FabLab-Merida/Smars-con-Microbit/CAD/SmarsMicrobit/Chasis/Servo/SMARS_servo_wheel.stl

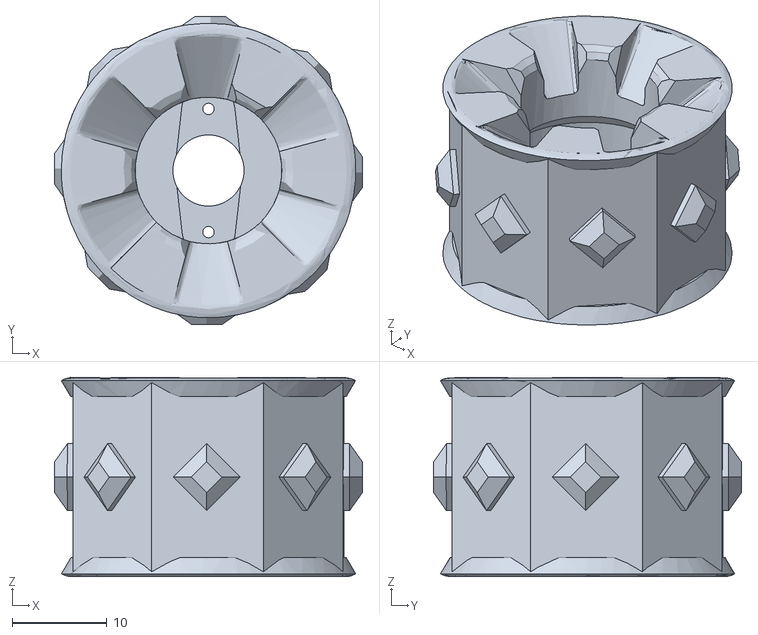
[picture p52: CAD file, 2024-05-20]
CAD/SmarsMicrobit/Chasis/Servo/SMARS_servo_wheel.stl
32.5 x 32.5 x 21.0
