FabLab-Merida/Smars-con-Microbit/CAD/SmarsMicrobit/CommonMicrobitPieces/slave_wheel_SL.stl

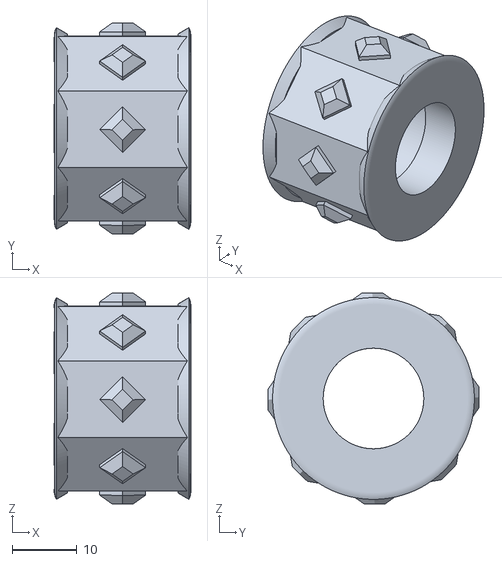
[picture p53: CAD file, 2024-05-20]
CAD/SmarsMicrobit/CommonMicrobitPieces/slave_wheel_SL.stl
21.0 x 32.5 x 32.5
