FabLab-Merida/Smars-con-Microbit/CAD/SmarsMicrobit/Sensores/Montacargas/fork_lift_a.stl

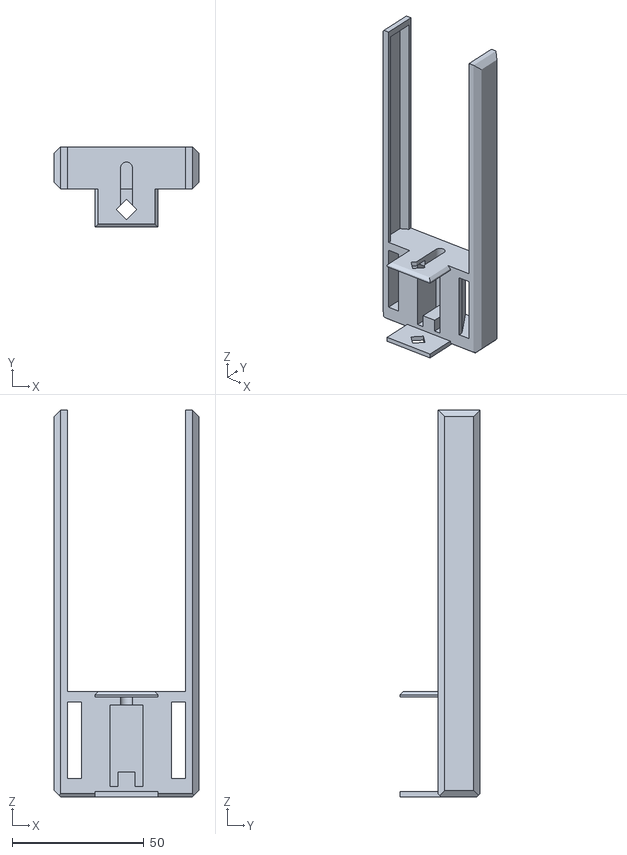
[picture p54: CAD file, 2024-05-20]
CAD/SmarsMicrobit/Sensores/Montacargas/fork_lift_a.stl
55.0 x 30.5 x 147.0
