FabLab-Merida/Smars-con-Microbit/CAD/SmarsMicrobit/Sensores/SensorCapacitivo/holder_soil_moisture.stl

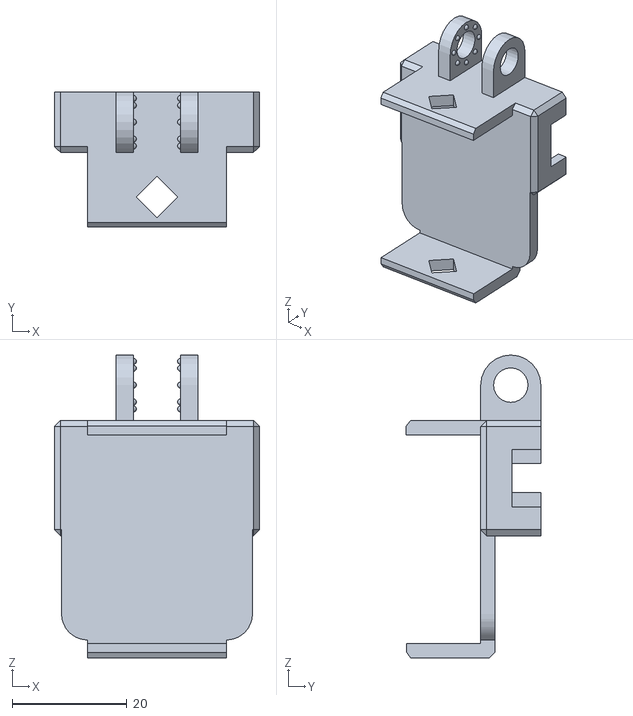
[picture p55: CAD file, 2024-05-20]
CAD/SmarsMicrobit/Sensores/SensorCapacitivo/holder_soil_moisture.stl
35.8 x 23.5 x 52.8
