FabLab-Merida/Smars-con-Microbit/CAD/SmarsMicrobit/Sensores/SensorUltrasonidos/ultrasonic_1.stl

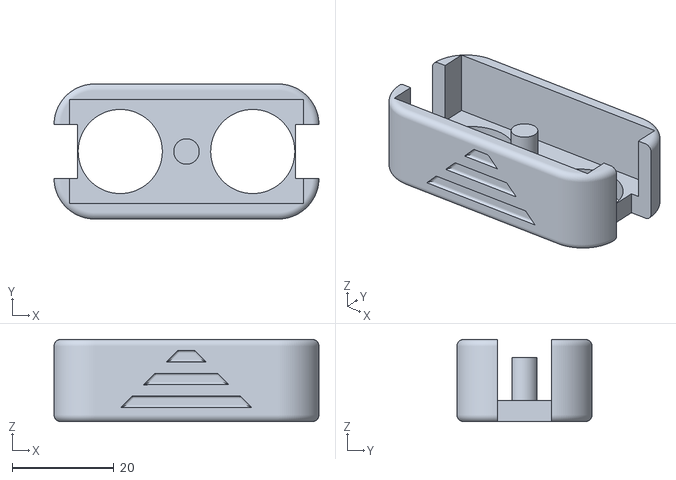
[picture p56: CAD file, 2024-05-20]
CAD/SmarsMicrobit/Sensores/SensorUltrasonidos/ultrasonic_1.stl
52.0 x 26.5 x 16.1
