FabLab-Merida/Smars-con-Microbit/CAD/SmarsMicrobit/Sensores/SmarsSensorCapacitivoV0(NoUsar)/Solid/smarsCapacitive.SLDPRT

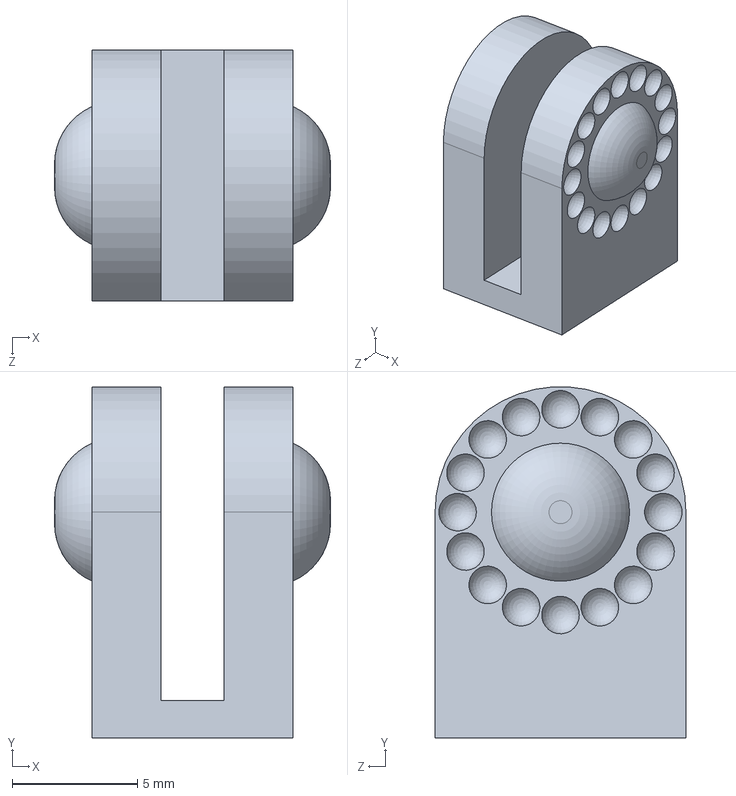
[picture p57: CAD file, 2024-05-20]
CAD/SmarsMicrobit/Sensores/SmarsSensorCapacitivoV0(NoUsar)/Solid/smarsCapacitive.SLDPRT
11.0 x 14.0 x 10.0 mm
