FabLab-Merida/Smars-con-Microbit/CAD/SmarsMicrobit/Chasis/PasoAPaso/SmarsMasterWheelStepper.stl

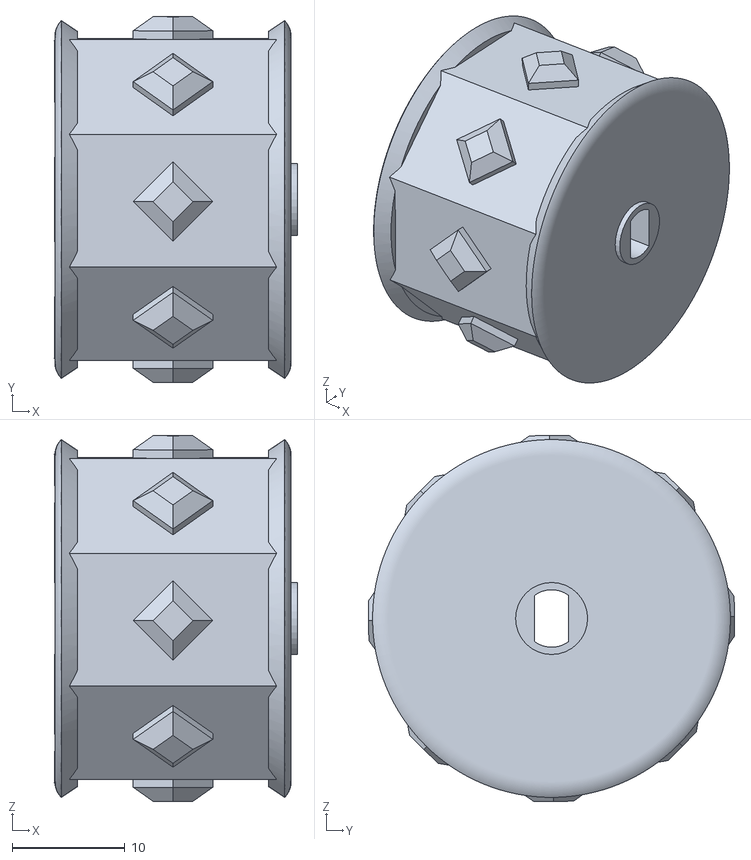
[picture p58: CAD file, 2024-05-20]
CAD/SmarsMicrobit/Chasis/PasoAPaso/SmarsMasterWheelStepper.stl
21.6 x 32.5 x 32.5
