FabLab-Merida/Smars-con-Microbit/CAD/SmarsMicrobit/CommonMicrobitPieces/mechanical_track.stl

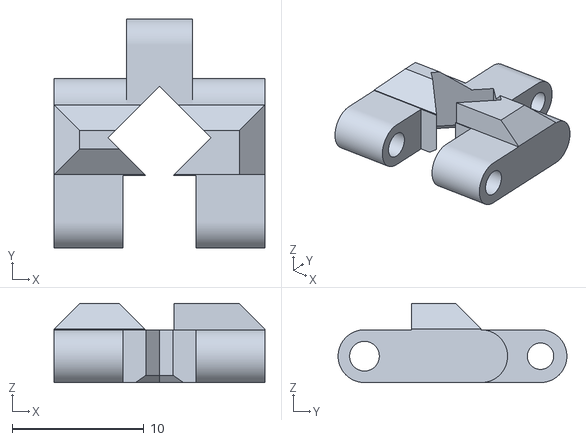
[picture p59: CAD file, 2024-05-20]
CAD/SmarsMicrobit/CommonMicrobitPieces/mechanical_track.stl
16.0 x 17.4 x 6.00
