FabLab-Merida/Smars-con-Microbit/CAD/SmarsMicrobit/Sensores/Montacargas/fork_lift_b.stl

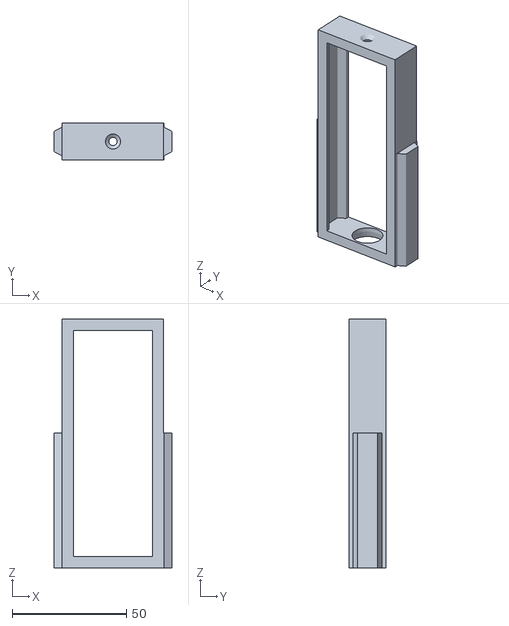
[picture p60: CAD file, 2024-05-20]
CAD/SmarsMicrobit/Sensores/Montacargas/fork_lift_b.stl
51.5 x 16.0 x 109.0
