FabLab-Merida/Smars-con-Microbit/CAD/SmarsMicrobit/Sensores/SmarsSensorCapacitivoV0(NoUsar)/STL/smarsCapacitive1.STL

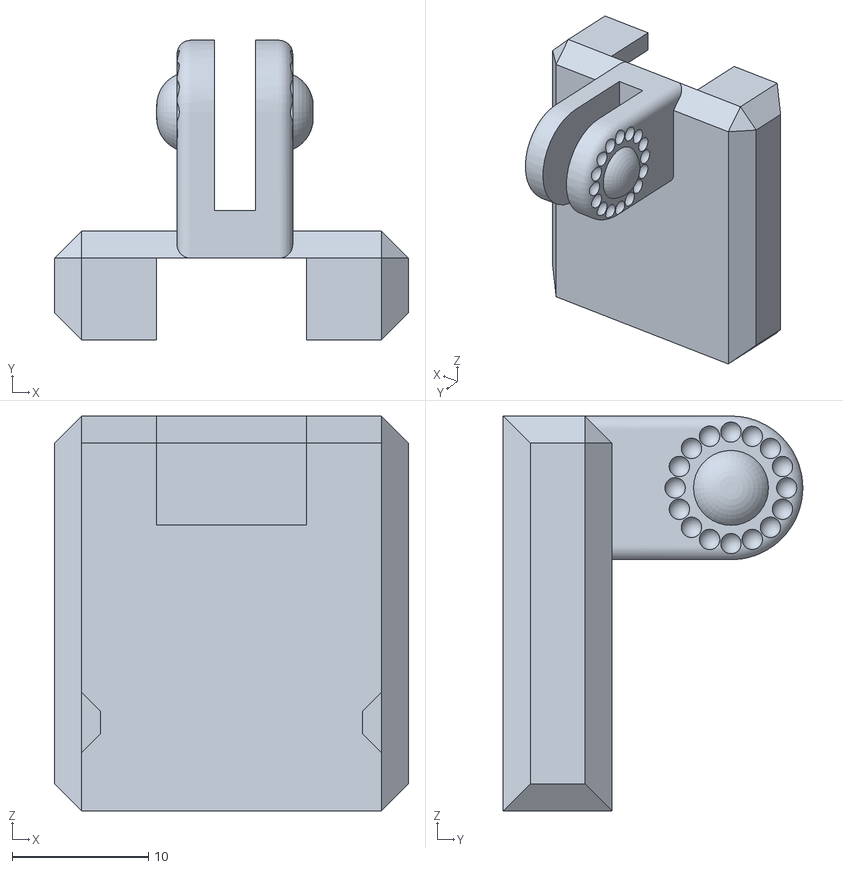
[picture p61: CAD file, 2024-05-20]
CAD/SmarsMicrobit/Sensores/SmarsSensorCapacitivoV0(NoUsar)/STL/smarsCapacitive1.STL
26.0 x 22.0 x 29.0
