FabLab-Merida/Smars-con-Microbit/CAD/SmarsMicrobit/Sensores/Montacargas/fork_lift_e.stl

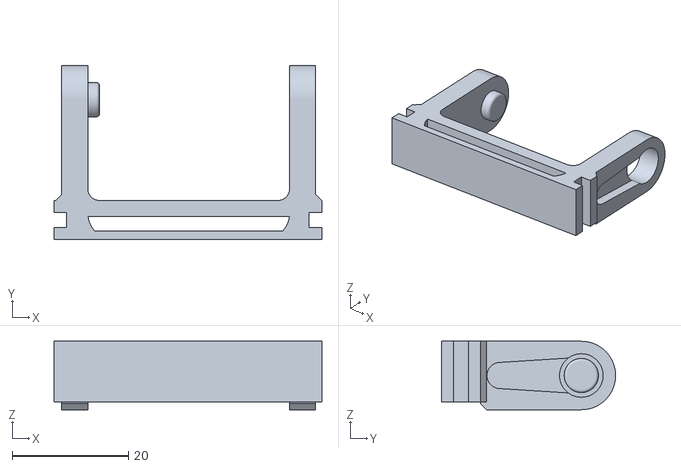
[picture p62: CAD file, 2024-05-20]
CAD/SmarsMicrobit/Sensores/Montacargas/fork_lift_e.stl
46.2 x 30.0 x 11.8
