FabLab-Merida/Smars-con-Microbit/CAD/SmarsMicrobit/Sensores/SensorCapacitivo/SmarsCapacitiveEdit.stl

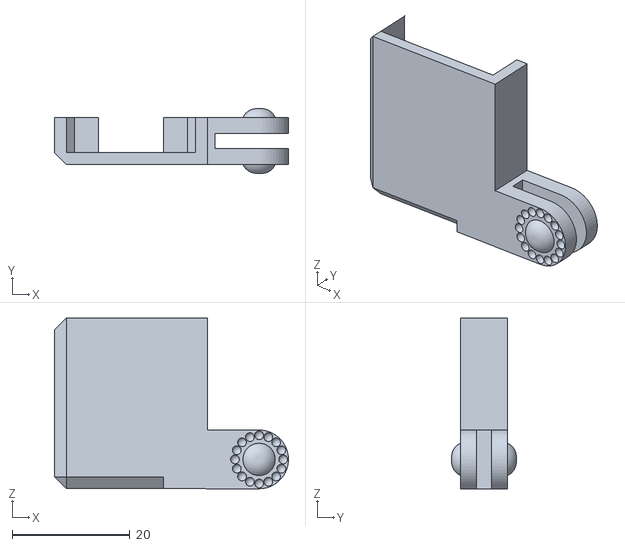
[picture p63: CAD file, 2024-05-20]
CAD/SmarsMicrobit/Sensores/SensorCapacitivo/SmarsCapacitiveEdit.stl
39.8 x 11.0 x 29.0
