FabLab-Merida/Smars-con-Microbit/CAD/SmarsMicrobit/Sensores/SmarsSensorCapacitivoV0(NoUsar)/STL/smarsCapacitive1Ez2Insert.stl

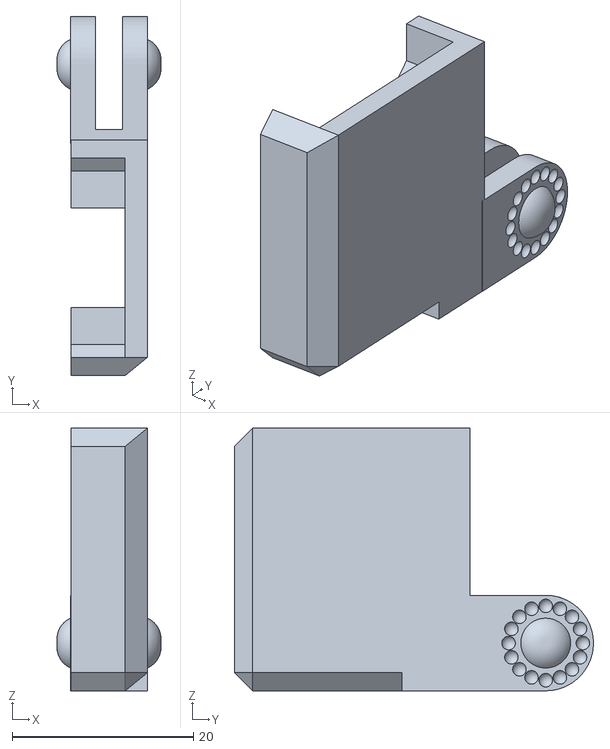
[picture p64: CAD file, 2024-05-20]
CAD/SmarsMicrobit/Sensores/SmarsSensorCapacitivoV0(NoUsar)/STL/smarsCapacitive1Ez2Insert.stl
11.5 x 39.6 x 29.0
