FabLab-Merida/Smars-con-Microbit/CAD/SmarsMicrobit/Sensores/Montacargas/fork_lift_f.stl

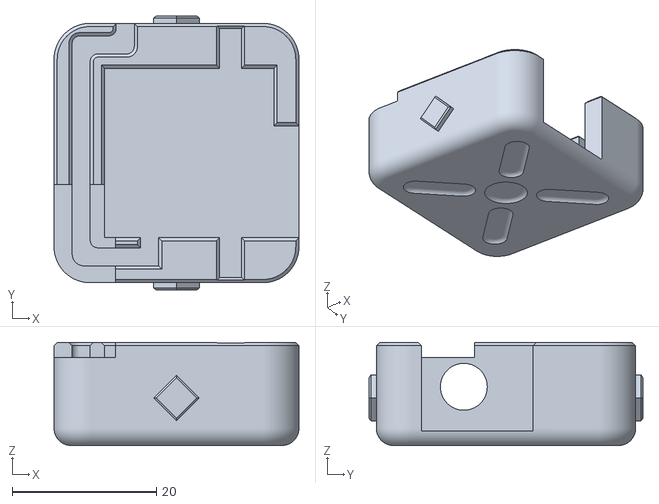
[picture p65: CAD file, 2024-05-20]
CAD/SmarsMicrobit/Sensores/Montacargas/fork_lift_f.stl
34.0 x 38.0 x 14.3
