FabLab-Merida/Smars-con-Microbit/CAD/SmarsMicrobit/Sensores/SmarsSensorCapacitivoV0(NoUsar)/Solid/smarsCapacitive1WOUTConnector.SLDPRT

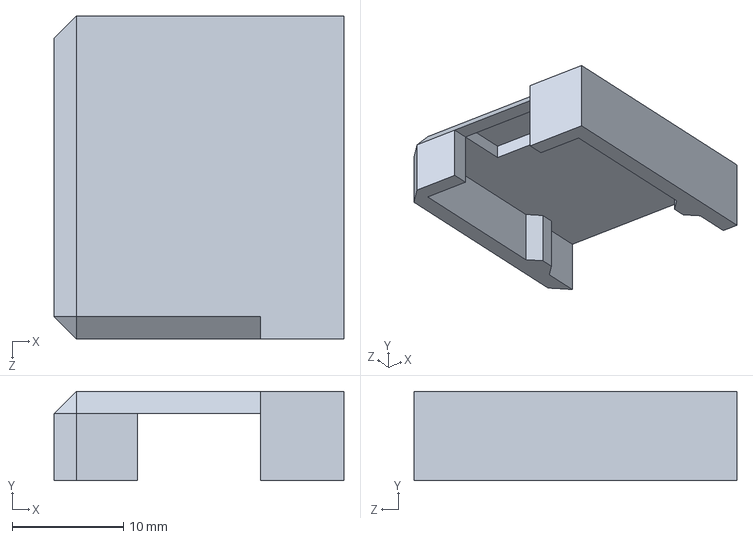
[picture p66: CAD file, 2024-05-20]
CAD/SmarsMicrobit/Sensores/SmarsSensorCapacitivoV0(NoUsar)/Solid/smarsCapacitive1WOUTConnector.SLDPRT
26.0 x 8.00 x 29.0 mm
