FabLab-Merida/Smars-con-Microbit/Code/InstalacionExtensionMakecode.PNG

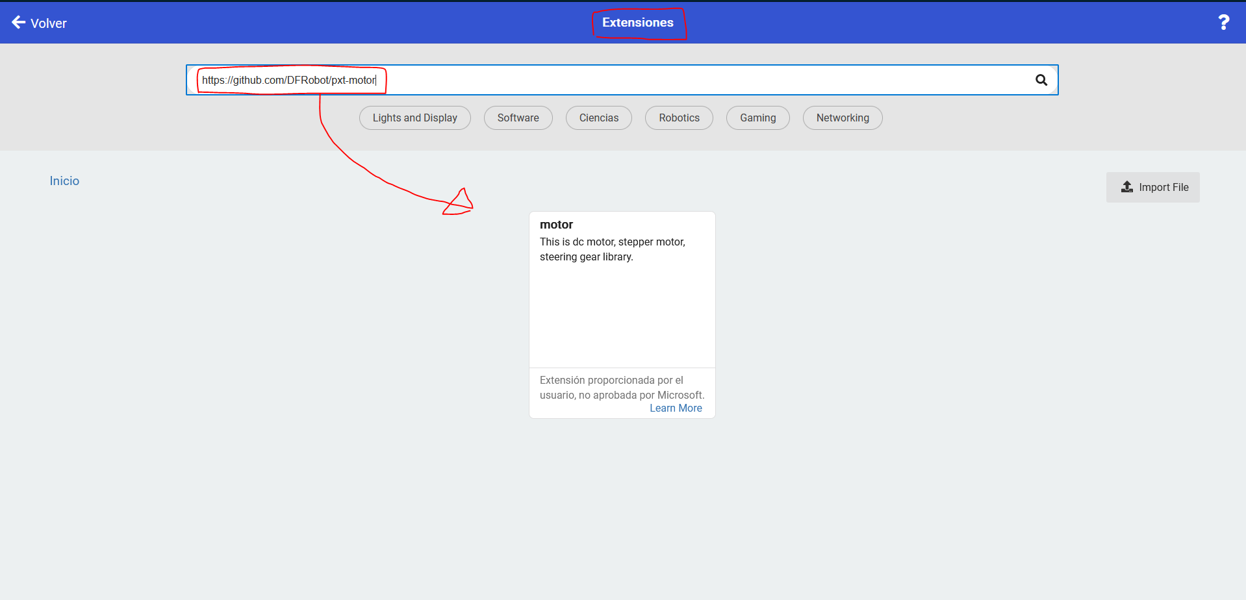
Code/InstalacionExtensionMakecode.PNG
